lucysrausch/charge-hf/media/3831.jpeg

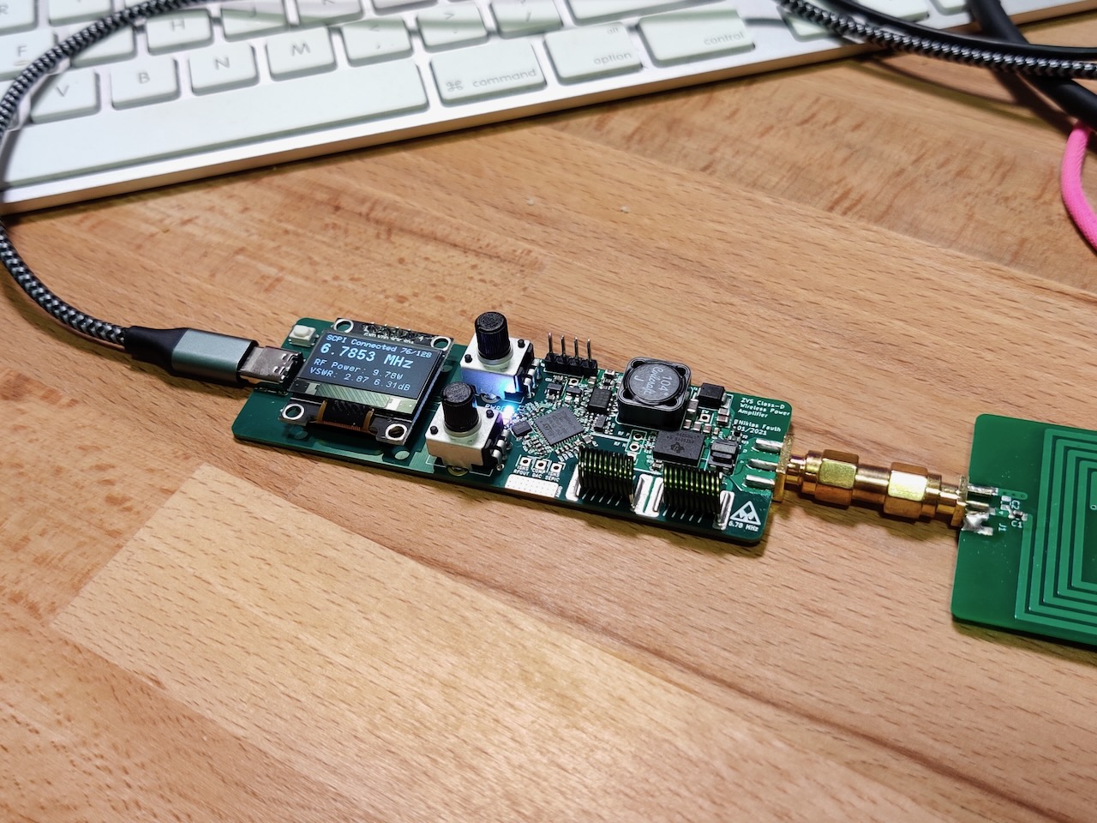
media/3831.jpeg
